marianol/simple6502/hardware/gallery/protoCard_PCB_back.jpg

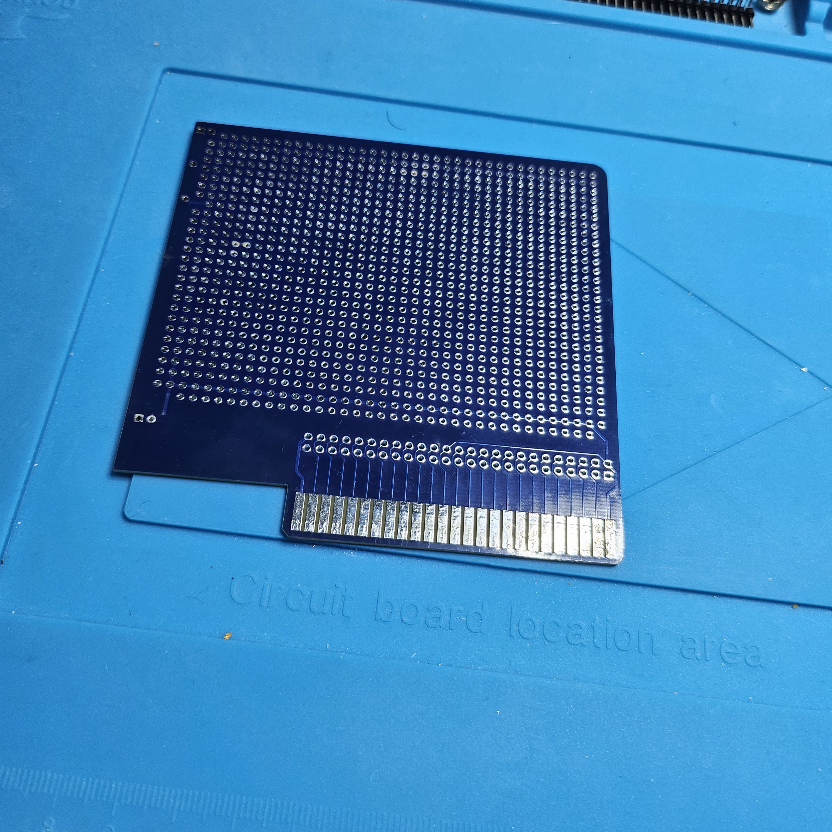
hardware/gallery/protoCard_PCB_back.jpg
