marianol/simple6502/hardware/schematics/6502motherboard_PCB.png

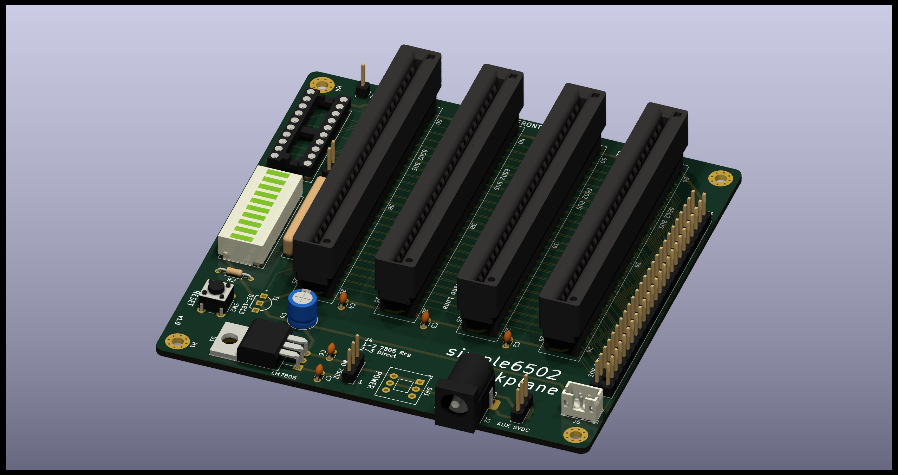
hardware/schematics/6502motherboard_PCB.png
