marianol/simple6502/hardware/schematics/6502motherboard_PCB_back.png

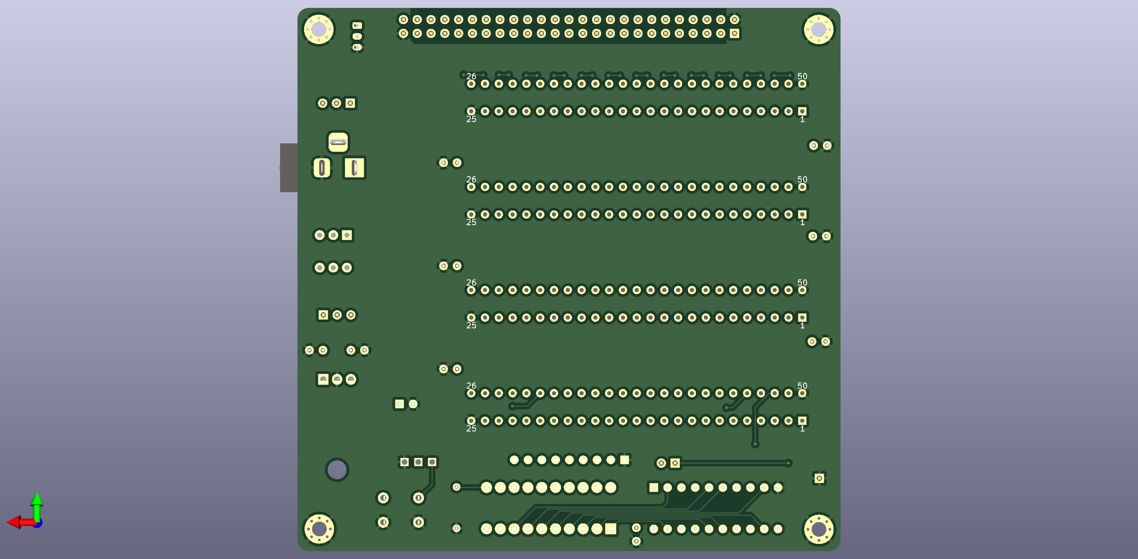
hardware/schematics/6502motherboard_PCB_back.png
