marianol/simple6502/hardware/schematics/6502motherboard_PCB_front.png

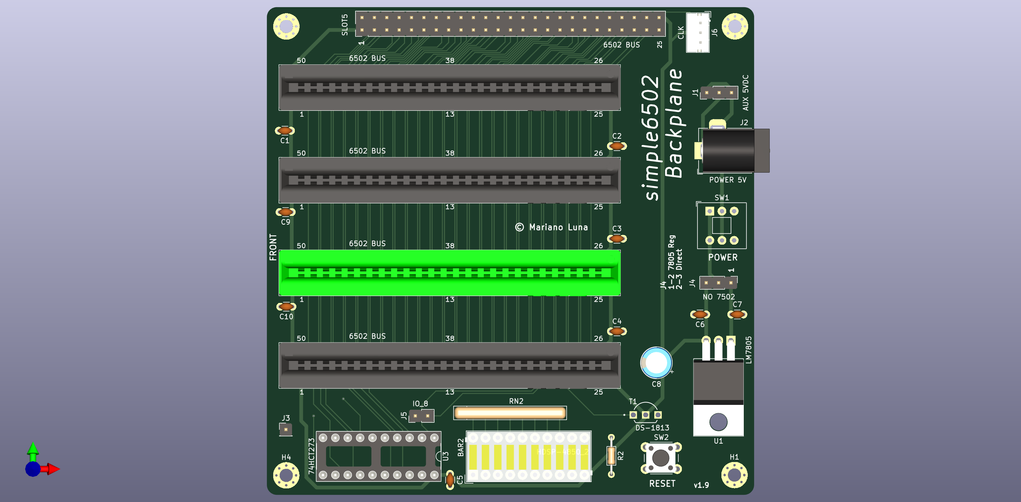
hardware/schematics/6502motherboard_PCB_front.png
