marianol/simple6502/hardware/schematics/simple6502_PCB_back.png

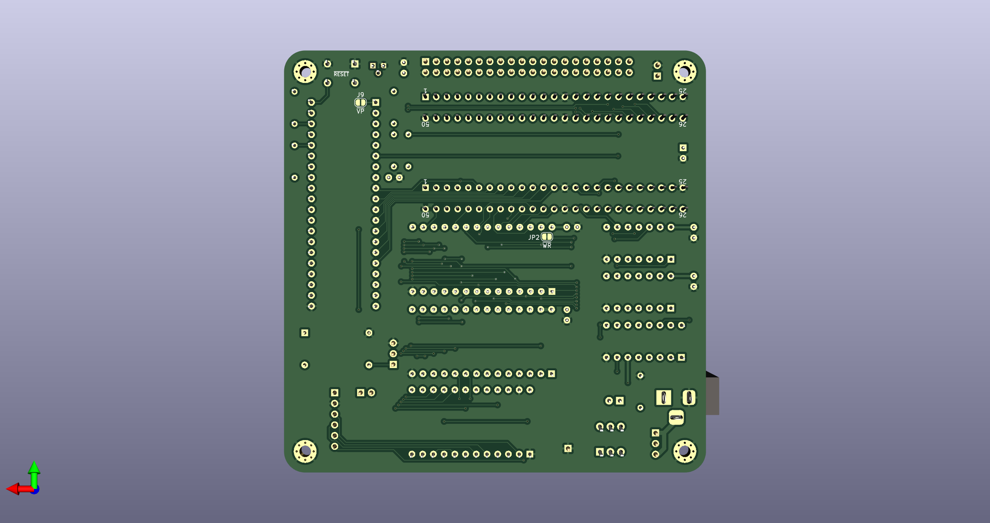
hardware/schematics/simple6502_PCB_back.png
