marianol/simple6502/hardware/schematics/simple6502_PCB_front_bare.png

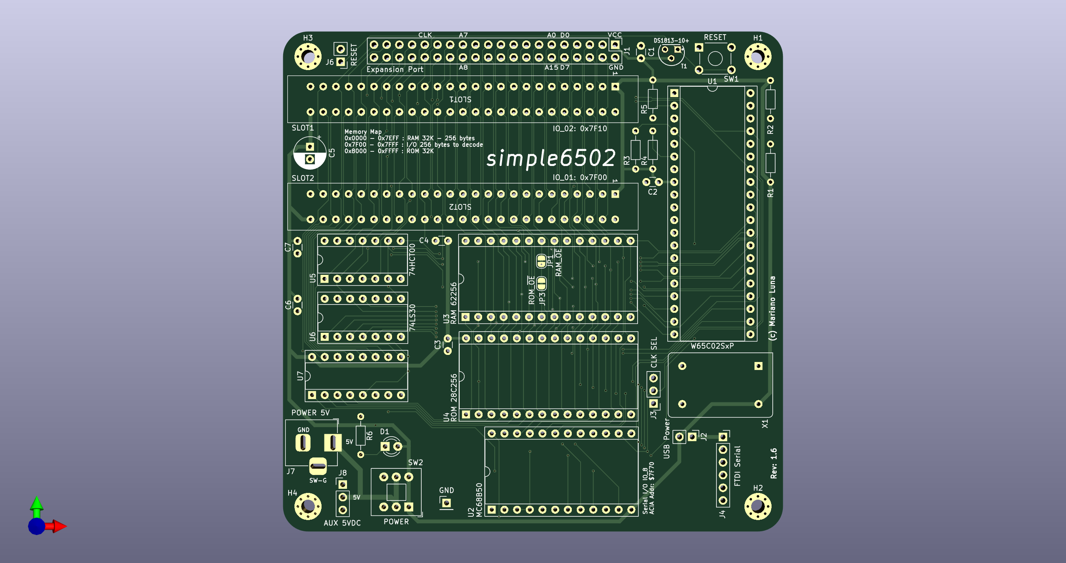
hardware/schematics/simple6502_PCB_front_bare.png
